nilsheuman/esp-mtx/gfx/aliexpress/display.png

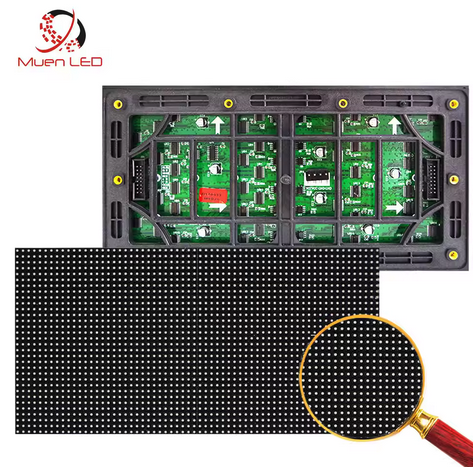
gfx/aliexpress/display.png
