nilsheuman/esp-mtx/gfx/aliexpress/esp32mini.png

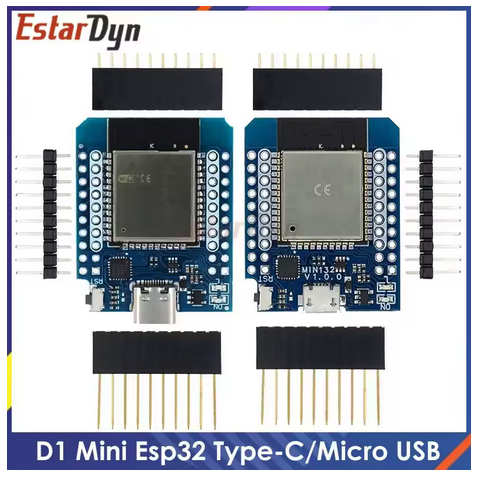
gfx/aliexpress/esp32mini.png
