nilsheuman/esp-mtx/gfx/aliexpress/jst-2pin.png

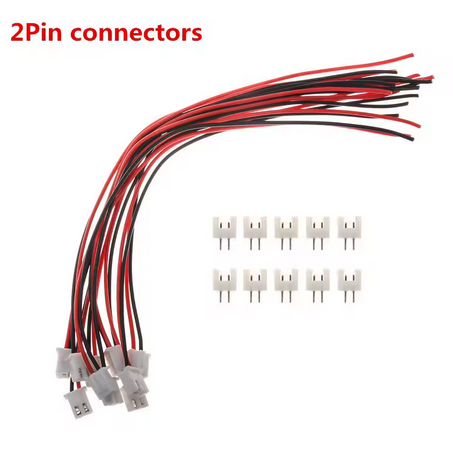
gfx/aliexpress/jst-2pin.png
