nilsheuman/esp-mtx/gfx/aliexpress/jst-5pin.png

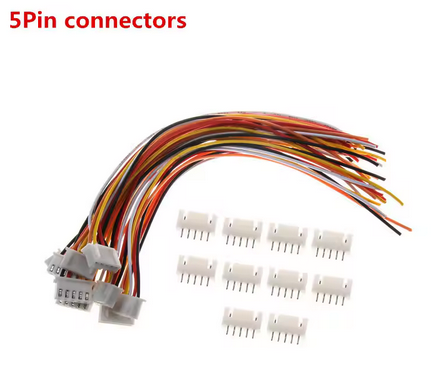
gfx/aliexpress/jst-5pin.png
