nilsheuman/esp-mtx/gfx/aliexpress/jst-diy.png

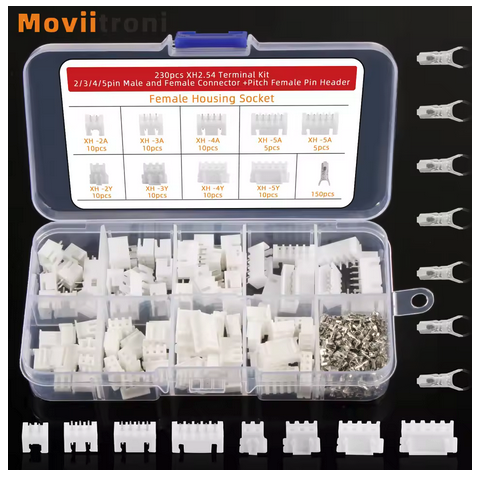
gfx/aliexpress/jst-diy.png
