nilsheuman/esp-mtx/gfx/rogue/rogue-led.jpg

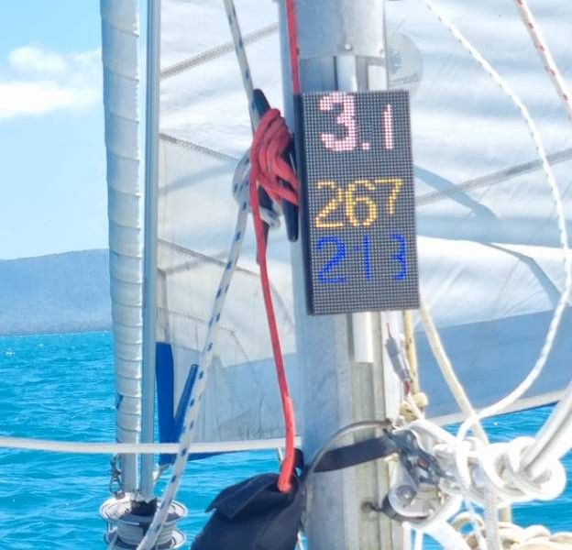
gfx/rogue/rogue-led.jpg
